biomurph/Mouse/Hardware/Wheel/Wheel.png

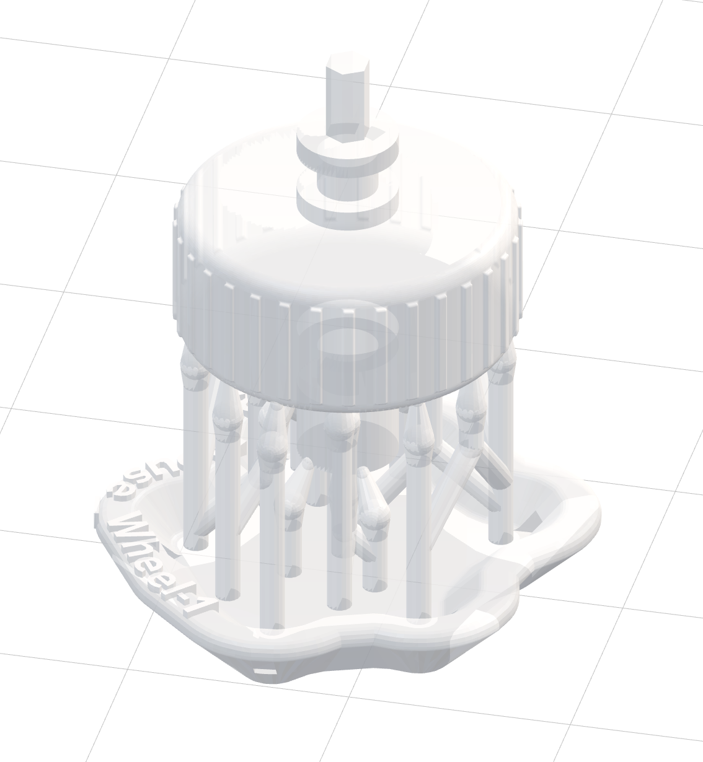
Hardware/Wheel/Wheel.png
