biomurph/Mouse/images/mousePrototype.jpg

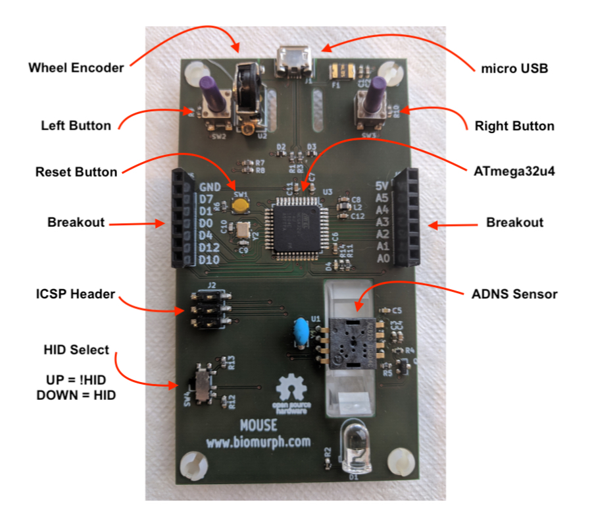
images/mousePrototype.jpg
