biomurph/Mouse/images/MouseParts-_0001_13.jpg

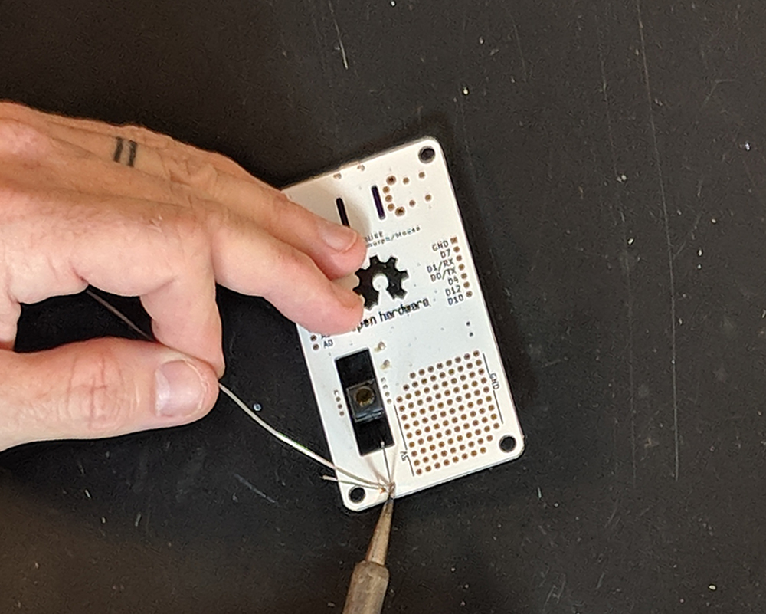
images/MouseParts-_0001_13.jpg
