biomurph/Mouse/images/MouseParts-_0004_09.jpg

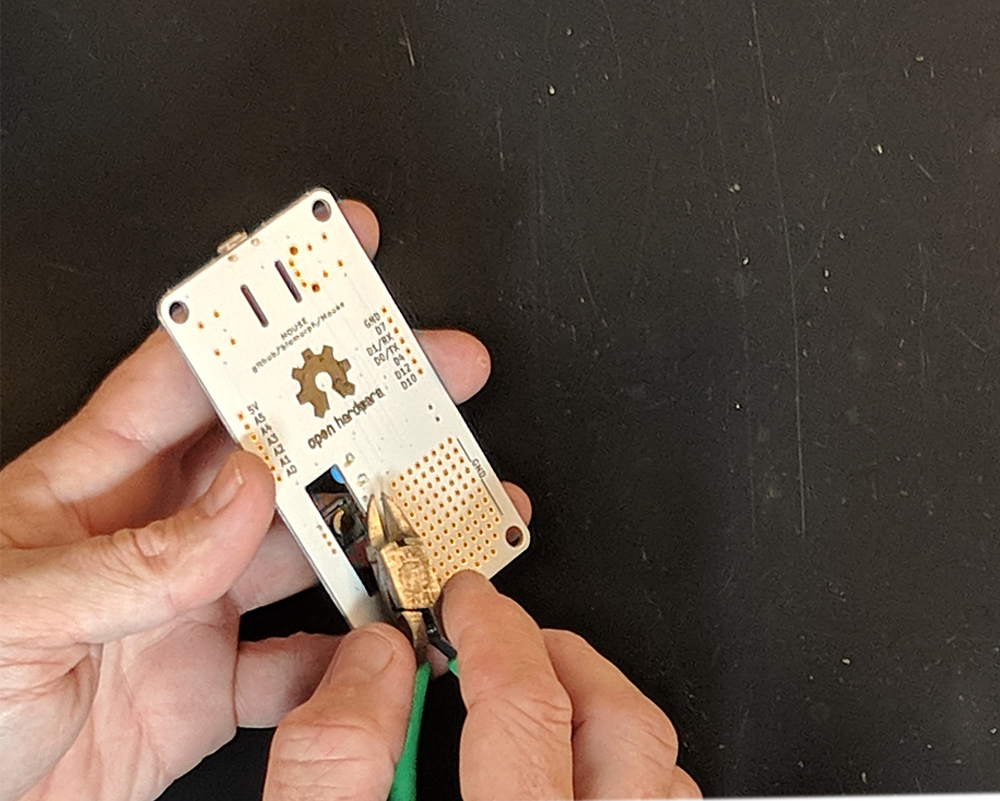
images/MouseParts-_0004_09.jpg
