biomurph/Mouse/images/MouseParts-_0005_08.jpg

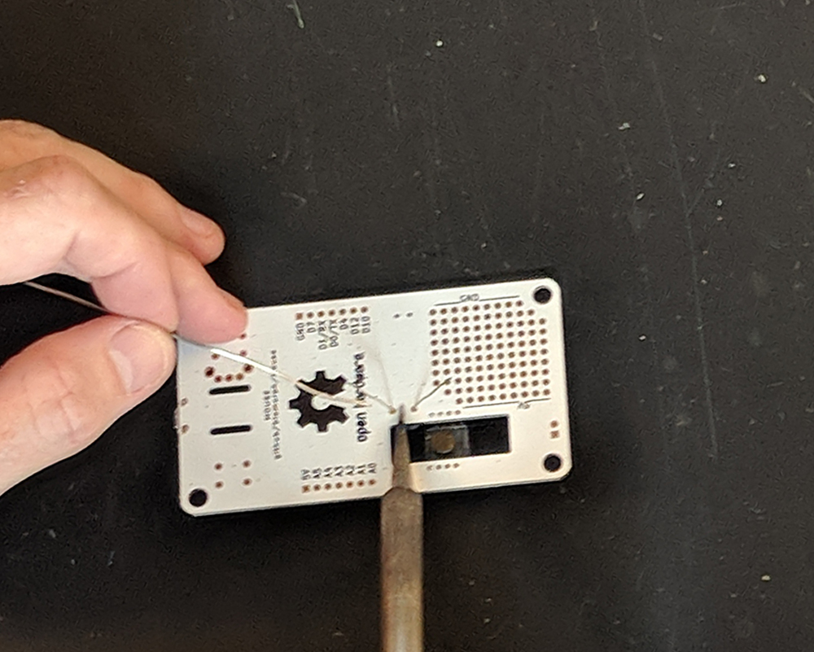
images/MouseParts-_0005_08.jpg
