biomurph/Mouse/images/MouseParts-_0007_06.jpg

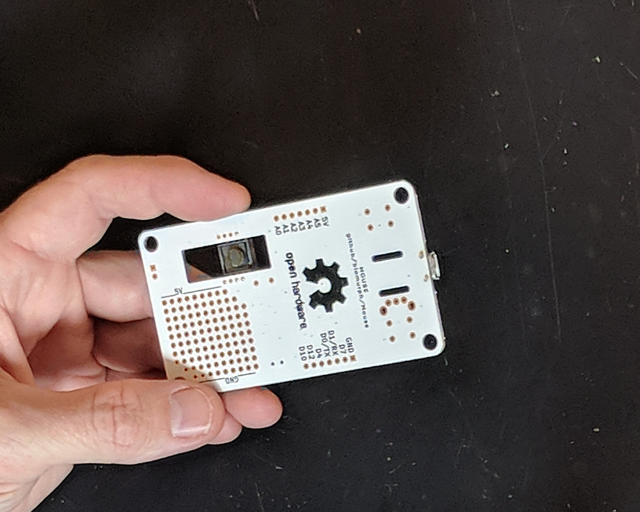
images/MouseParts-_0007_06.jpg
