biomurph/Mouse/images/MouseParts-_0013_39.jpg

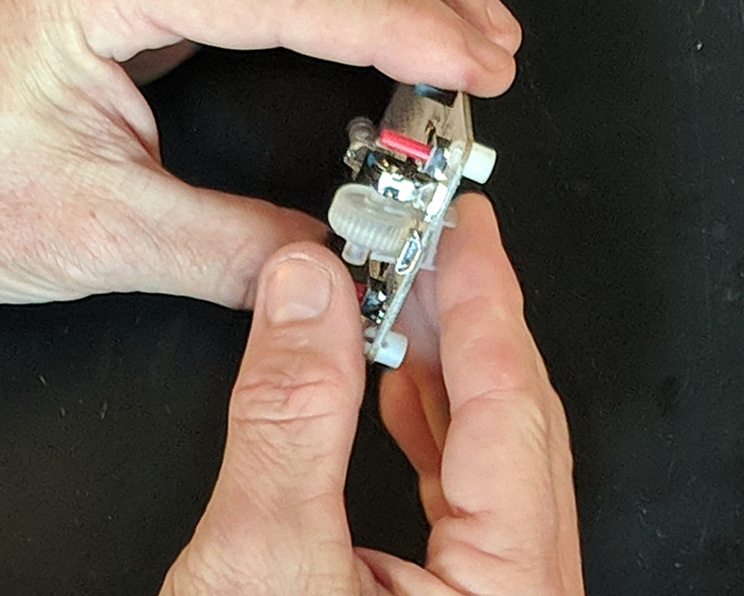
images/MouseParts-_0013_39.jpg
