biomurph/Mouse/images/MouseParts-_0018_34.jpg

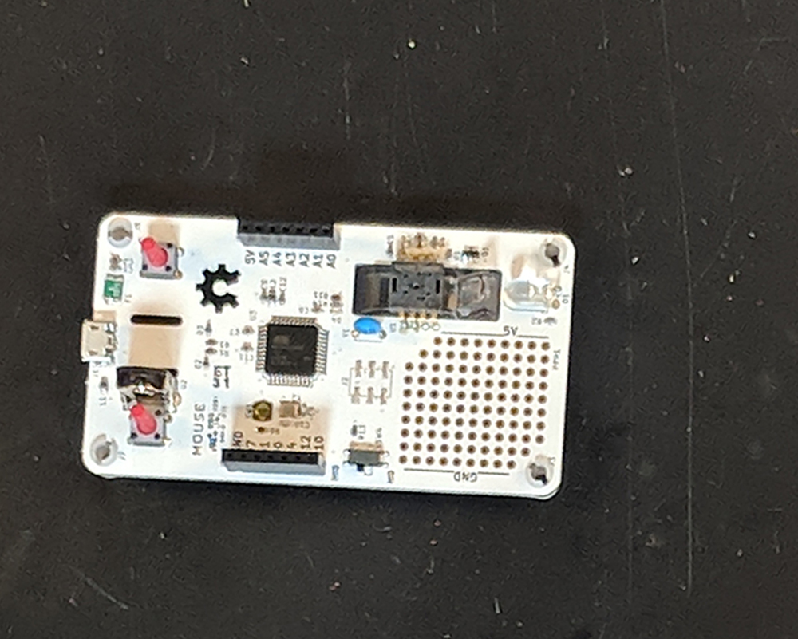
images/MouseParts-_0018_34.jpg
