biomurph/Mouse/images/MouseParts-_0021_42.jpg

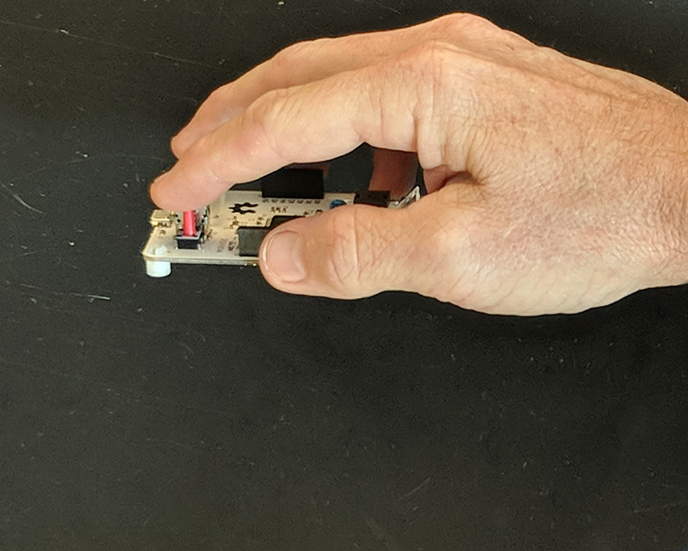
images/MouseParts-_0021_42.jpg
