biomurph/Mouse/images/MouseParts-_0025_26.jpg

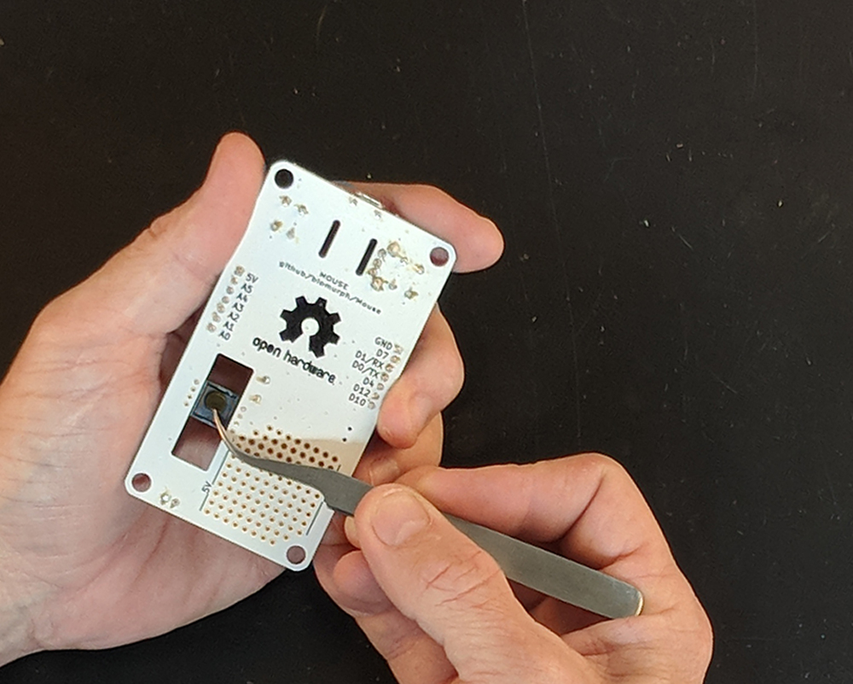
images/MouseParts-_0025_26.jpg
