biomurph/Mouse/images/MouseParts-_0029_18.jpg

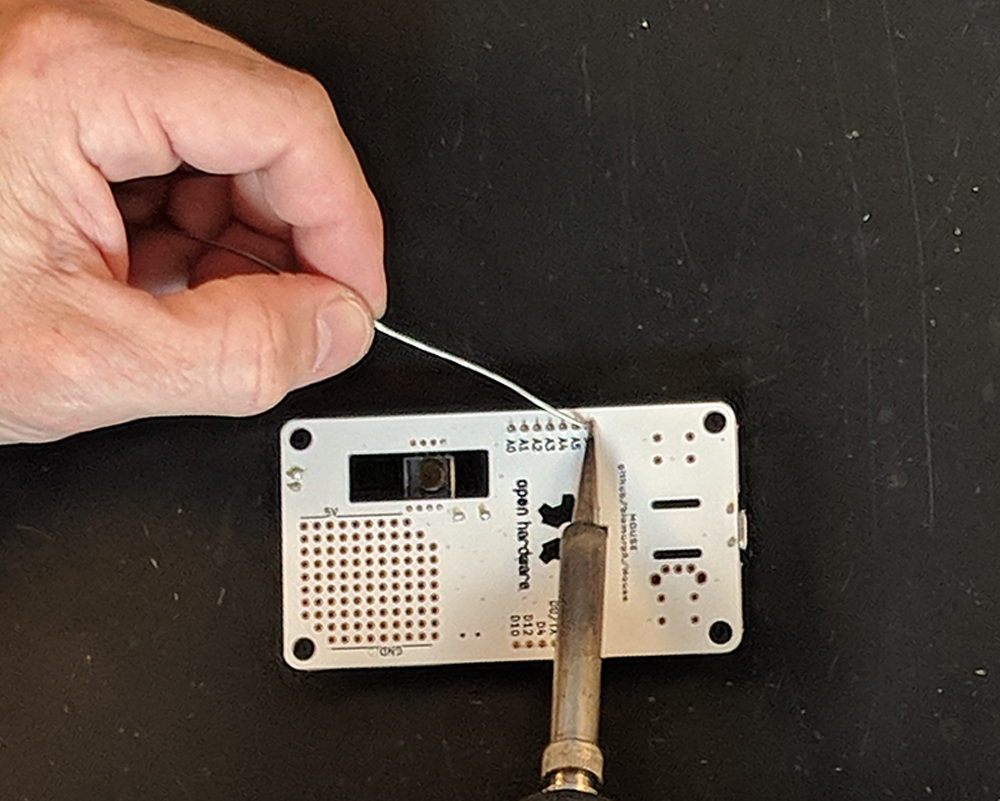
images/MouseParts-_0029_18.jpg
