biomurph/Mouse/images/MouseParts-_0032_01.jpg

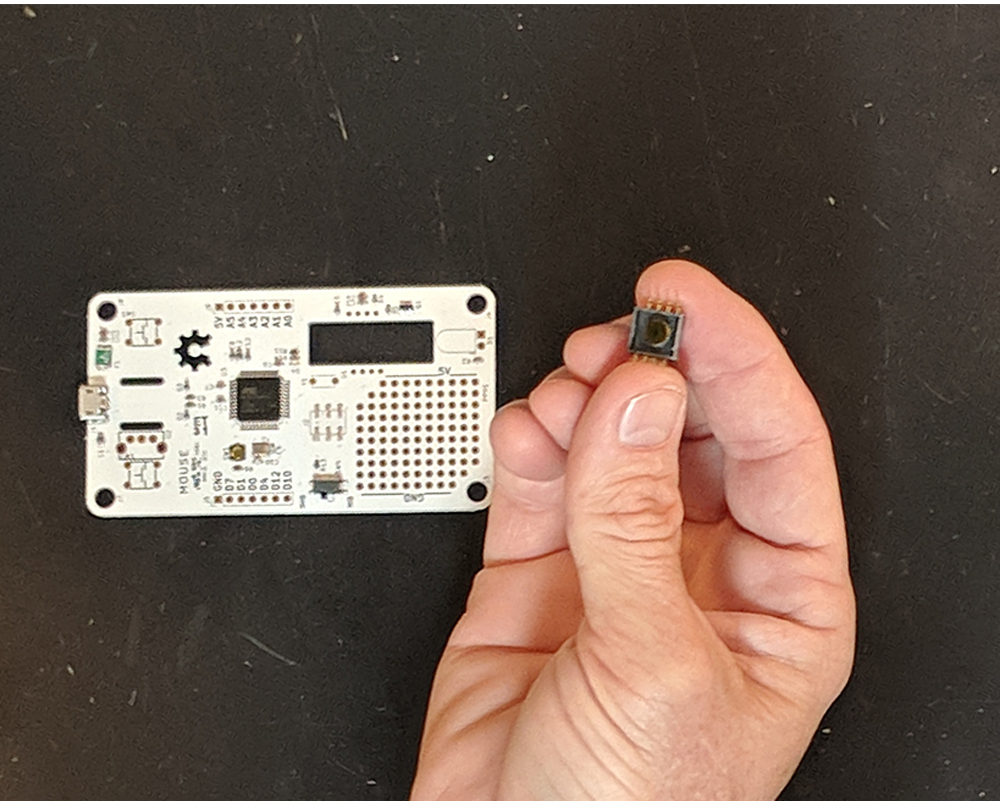
images/MouseParts-_0032_01.jpg
