biomurph/Mouse/images/MouseParts-_0033_02.jpg

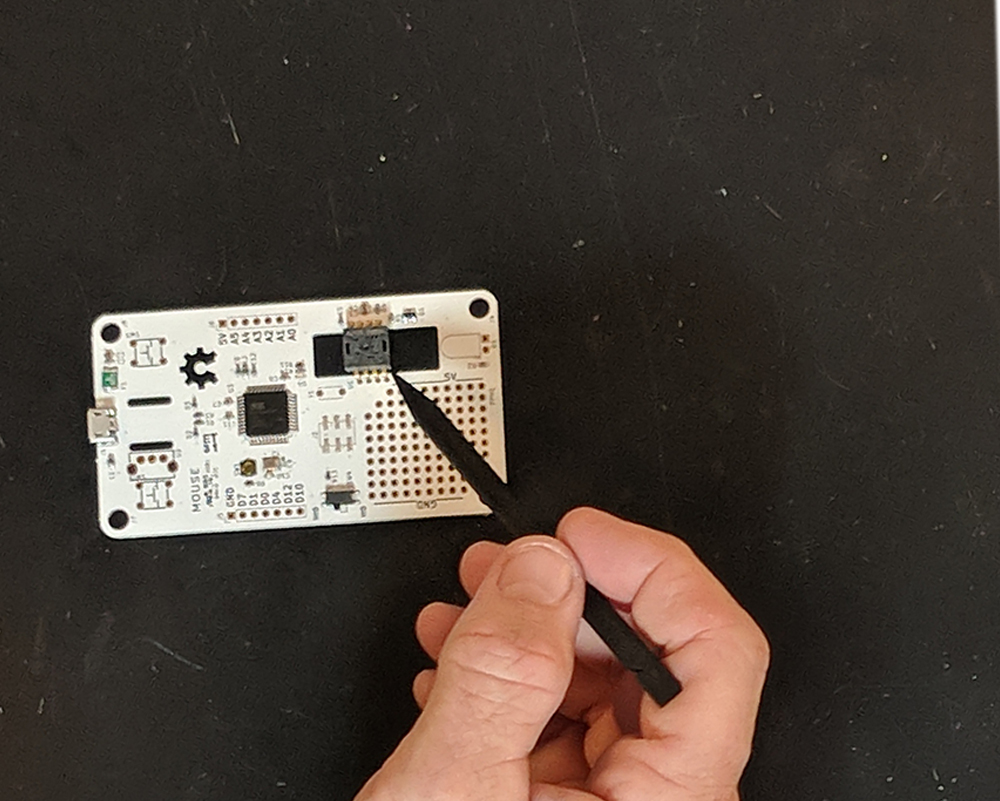
images/MouseParts-_0033_02.jpg
