biomurph/Mouse/images/MouseParts-_0034_03.jpg

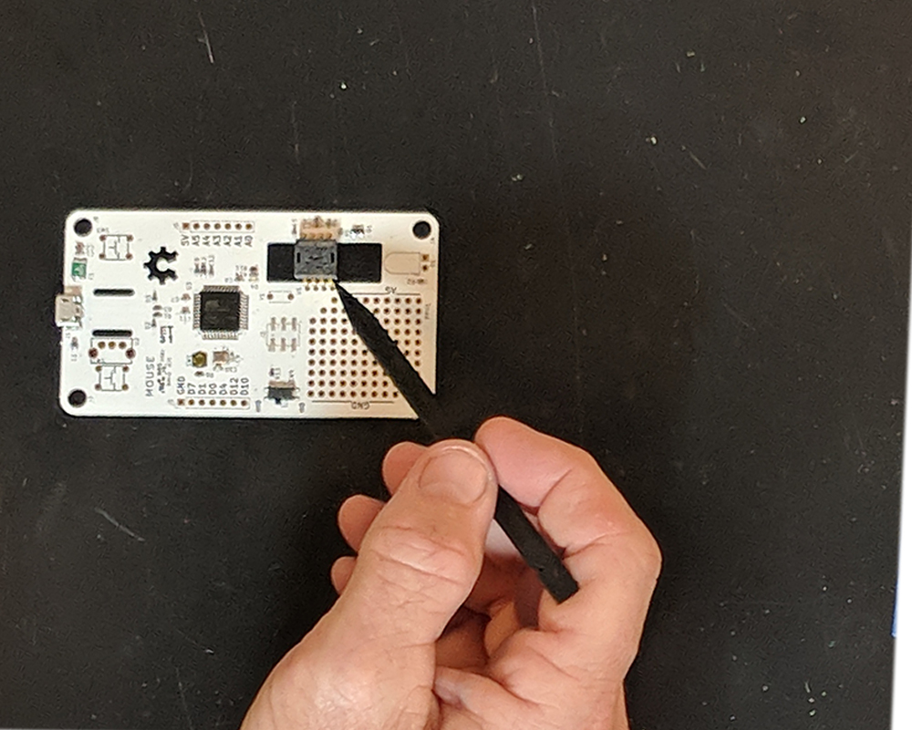
images/MouseParts-_0034_03.jpg
