biomurph/Mouse/images/MouseParts-_0035_04.jpg

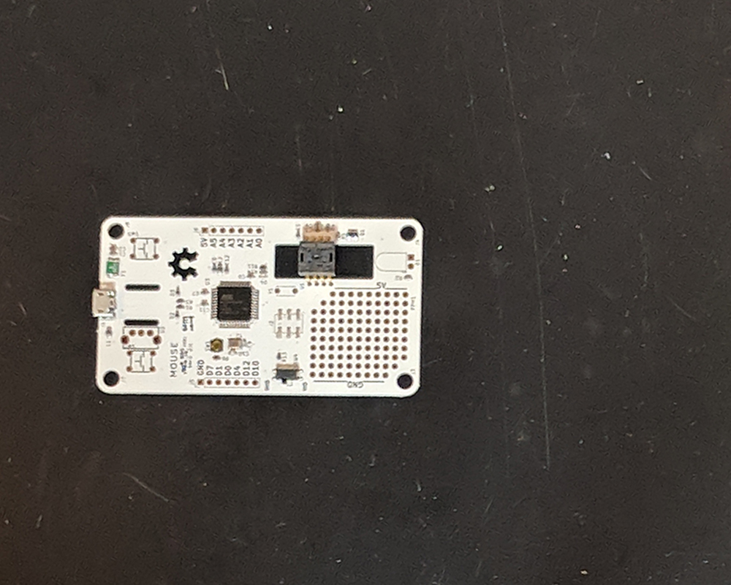
images/MouseParts-_0035_04.jpg
