biomurph/Mouse/images/MouseParts-_0036_05.jpg

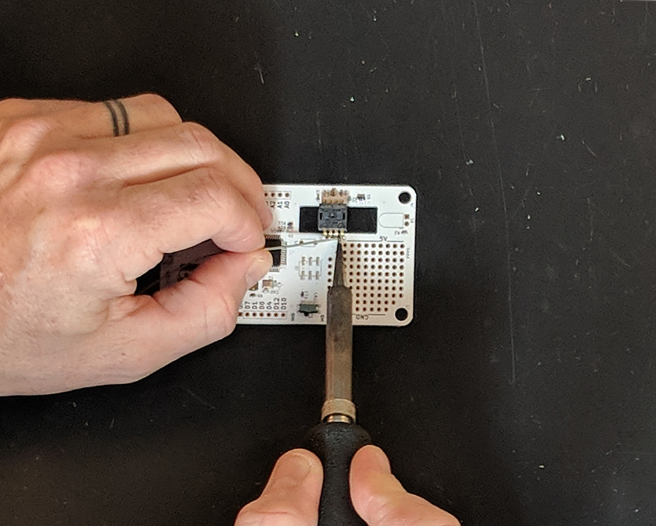
images/MouseParts-_0036_05.jpg
