biomurph/Mouse/images/MouseParts-_0037_06.jpg

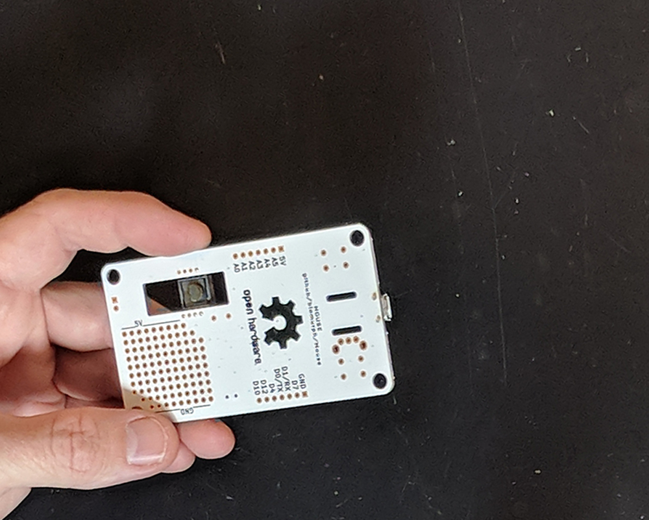
images/MouseParts-_0037_06.jpg
