biomurph/Mouse/images/MouseParts-_0038_07.jpg

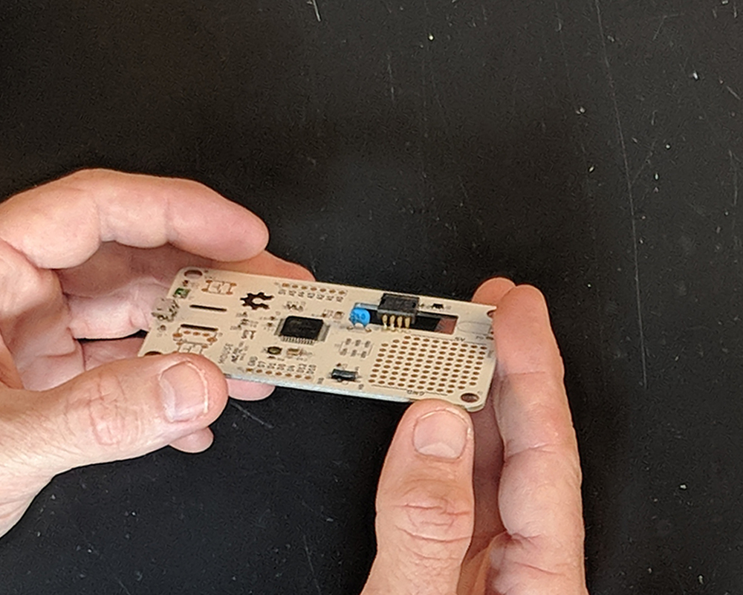
images/MouseParts-_0038_07.jpg
