biomurph/Mouse/images/MouseParts-_0039_08.jpg

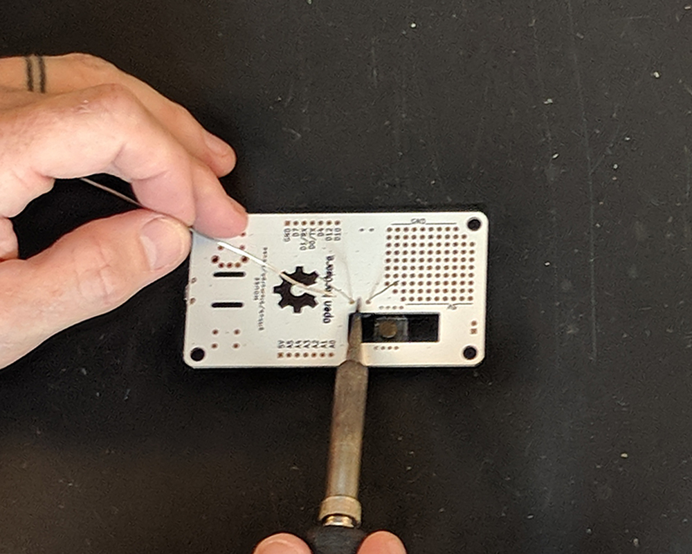
images/MouseParts-_0039_08.jpg
