biomurph/Mouse/images/MouseParts-_0040_09.jpg

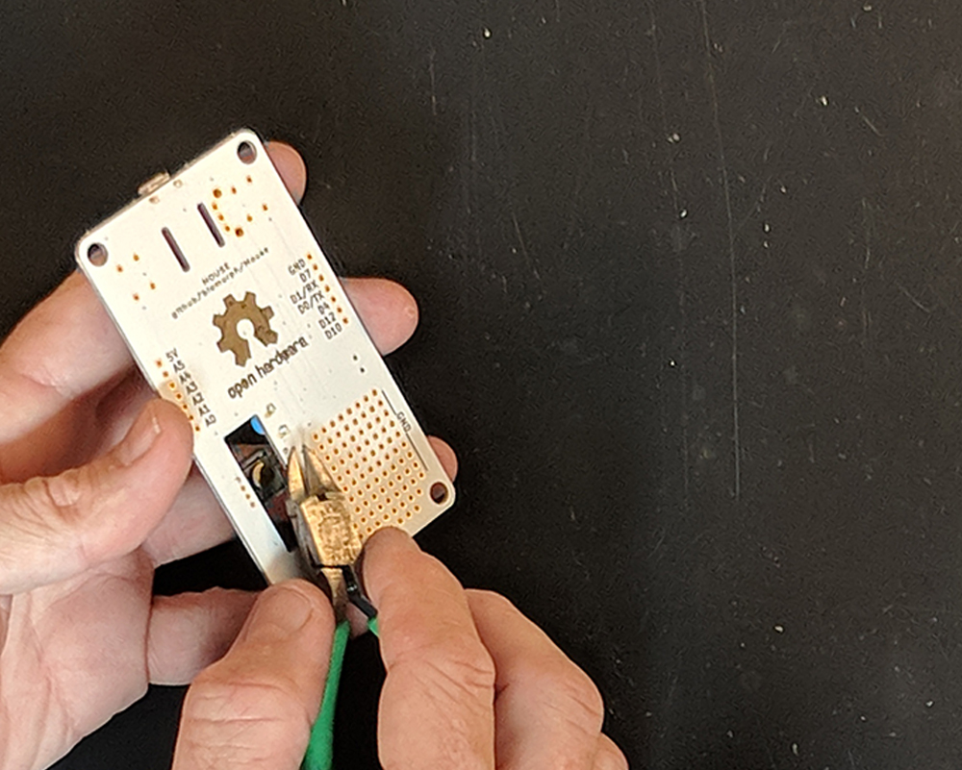
images/MouseParts-_0040_09.jpg
