biomurph/Mouse/images/MouseParts-_0042_13.jpg

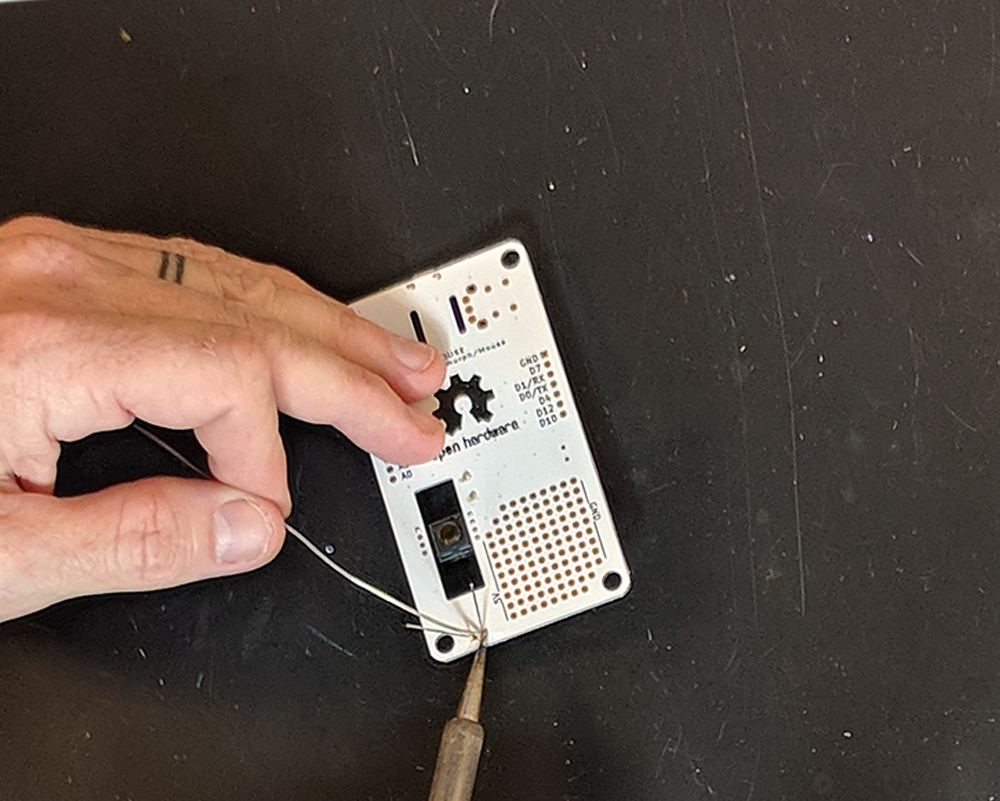
images/MouseParts-_0042_13.jpg
