biomurph/Mouse/images/MouseParts-_0043_14.jpg

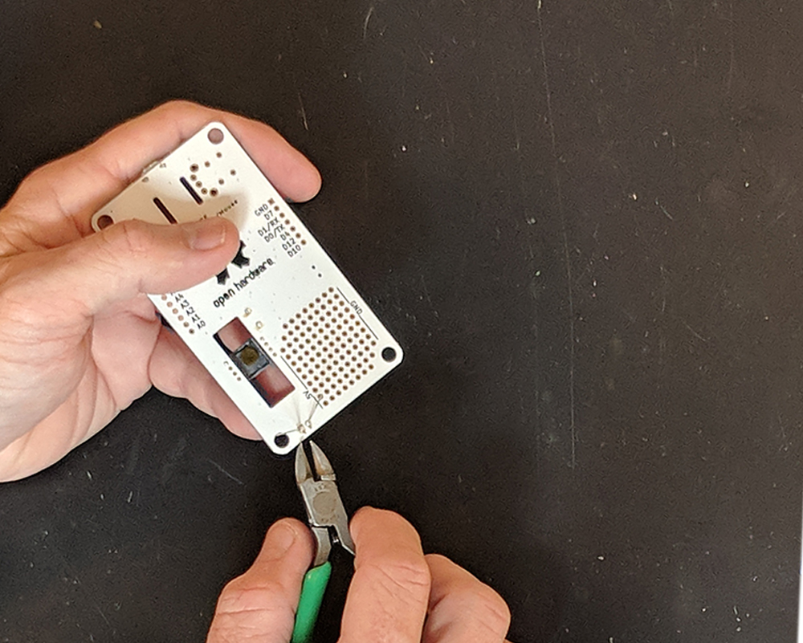
images/MouseParts-_0043_14.jpg
